jmA500/trapdoor5/doc/gary-t4-pins-socket.jpg

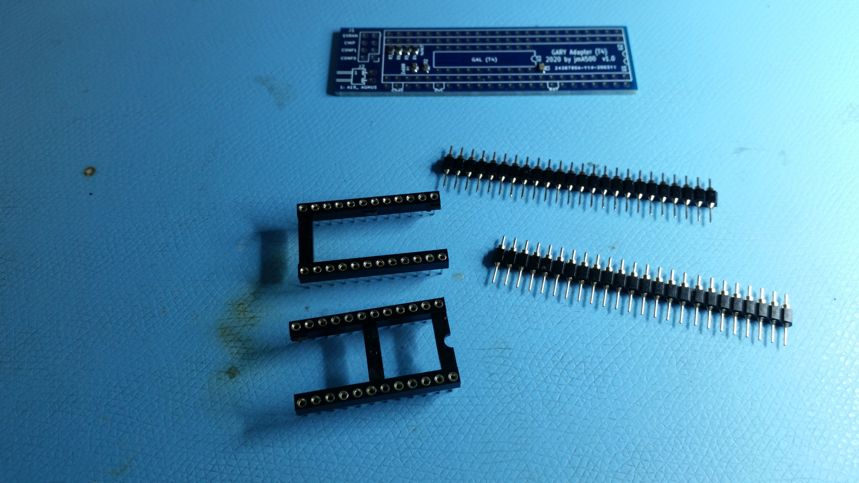
doc/gary-t4-pins-socket.jpg
