jmA500/trapdoor5/doc/plcc-socket.jpg

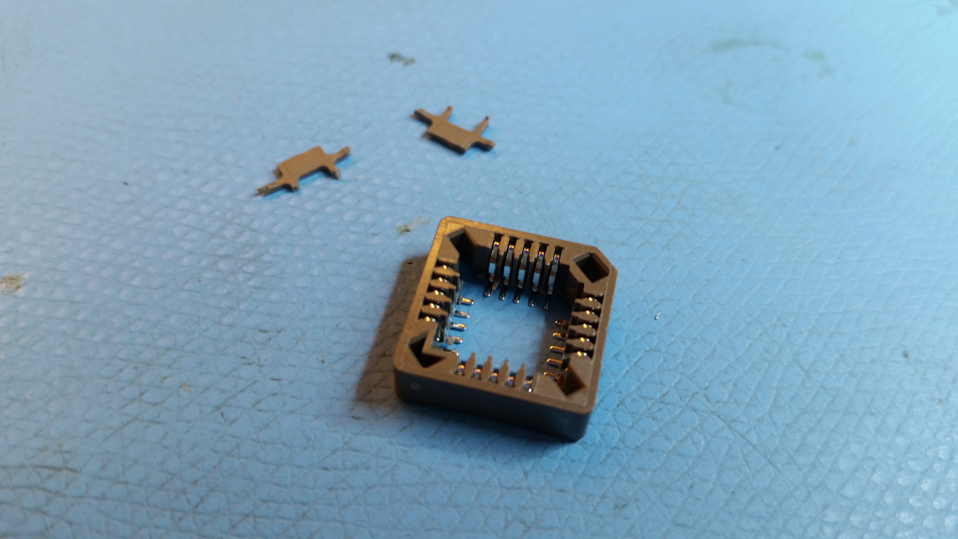
doc/plcc-socket.jpg
